jp112sdl/WemosD1_HomeMatic_RGBTouch/RGBhorz_halb.c

#include <pgmspace.h>

#if defined(__AVR__)
#include <avr/pgmspace.h>
#elif defined(__PIC32MX__)
#define PROGMEM
#elif defined(__arm__)
#define PROGMEM
#endif

const unsigned short RGBhorz_halb[27948] PROGMEM = {
  0xF863, 0xF883, 0xF883, 0xF8A3, 0xF8A3, 0xF8C3, 0xF8C3, 0xF8C3, 0xF8E3, 0xF903, 0xF903, 0xF923, 0xF923, 0xF943, 0xF963, 0xF963,   // 0x0010 (16) pixels
  0xF983, 0xF983, 0xF9A3, 0xF9C3, 0xF9C3, 0xF9E3, 0xFA03, 0xFA03, 0xFA23, 0xFA43, 0xFA43, 0xFA63, 0xFA63, 0xFA83, 0xFAA3, 0xFAC3,   // 0x0020 (32) pixels
  0xFAC3, 0xFAE3, 0xFB04, 0xFB04, 0xFB24, 0xFB44, 0xFB44, 0xFB64, 0xFB64, 0xFB84, 0xFBA4, 0xFBC4, 0xFBC4, 0xFBE4, 0xFC04, 0xFC24,   // 0x0030 (48) pixels
  0xFC24, 0xFC44, 0xFC64, 0xFC64, 0xFC84, 0xFC84, 0xFCA4, 0xFCC4, 0xFCC4, 0xFCE4, 0xFD05, 0xFD25, 0xFD25, 0xFD45, 0xFD45, 0xFD65,   // 0x0040 (64) pixels
  0xFD85, 0xFDA5, 0xFDA5, 0xFDC5, 0xFDE5, 0xFDE5, 0xFE05, 0xFE25, 0xFE25, 0xFE45, 0xFE65, 0xFE85, 0xFE86, 0xFEA6, 0xFEC6, 0xFEC6,   // 0x0050 (80) pixels
  0xFEE6, 0xFF06, 0xFF06, 0xFF26, 0xFF26, 0xFF46, 0xFF66, 0xFF86, 0xFF86, 0xFFA6, 0xFFC6, 0xFFC6, 0xFFE6, 0xFFE6, 0xFFE6, 0xF7E6,   // 0x0060 (96) pixels
  0xF7E6, 0xEFE6, 0xEFE6, 0xEFE6, 0xE7E6, 0xE7E6, 0xE7E6, 0xDFE6, 0xDFE6, 0xDFE6, 0xD7E6, 0xD7E6, 0xD7E6, 0xCFE6, 0xCFE6, 0xC7E6,   // 0x0070 (112) pixels
  0xC7E6, 0xC7E6, 0xBFE6, 0xBFE6, 0xBFE6, 0xB7E6, 0xB7E6, 0xB7E6, 0xAFE6, 0xAFE6, 0xAFE6, 0xA7E6, 0xA7E6, 0x9FE6, 0x9FE6, 0x9FE6,   // 0x0080 (128) pixels
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
  0x2FE9, 0x2FE9, 0x2FEA, 0x2FEA, 0x2FEA, 0x2FEA, 0x2FEB, 0x2FEB, 0x2FEB, 0x2FEB, 0x2FEC, 0x2FEC, 0x2FEC, 0x2FED, 0x2FED, 0x2FED,   // 0x2FF0 (12272) pixels
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
