jp112sdl/WemosD1_HomeMatic_RGBTouch/OTA.ino

void startOTAhandling() {
  Serial.println("Starte OTA-Handler...");
  ArduinoOTA.onStart([]() {
    Serial.println(F("Start updating"));
  });
  ArduinoOTA.onEnd([]() {
    Serial.println(F("Update done."));
  });
  ArduinoOTA.onProgress([](unsigned int progress, unsigned int total) {
    //Serial.printf(".");
  });
  ArduinoOTA.onError([](ota_error_t error) {
    Serial.println("Error " + String(error) + ": ");
    if (error == OTA_AUTH_ERROR) Serial.println("Auth Failed");
    else if (error == OTA_BEGIN_ERROR) Serial.println("Begin Failed");
    else if (error == OTA_CONNECT_ERROR) Serial.println("Connect Failed");
    else if (error == OTA_RECEIVE_ERROR) Serial.println("Receive Failed");
    else if (error == OTA_END_ERROR) Serial.println("End Failed");
  });

  ArduinoOTA.setHostname(Hostname);
  ArduinoOTA.begin();
}
